HO44-PROJECT/MrJ-HO-scale-DB-style-Era-III-Train-Signals-Electronics/release/kicad_pcb_ho_db_signals_breadboard_v3 - pcb parameters.png

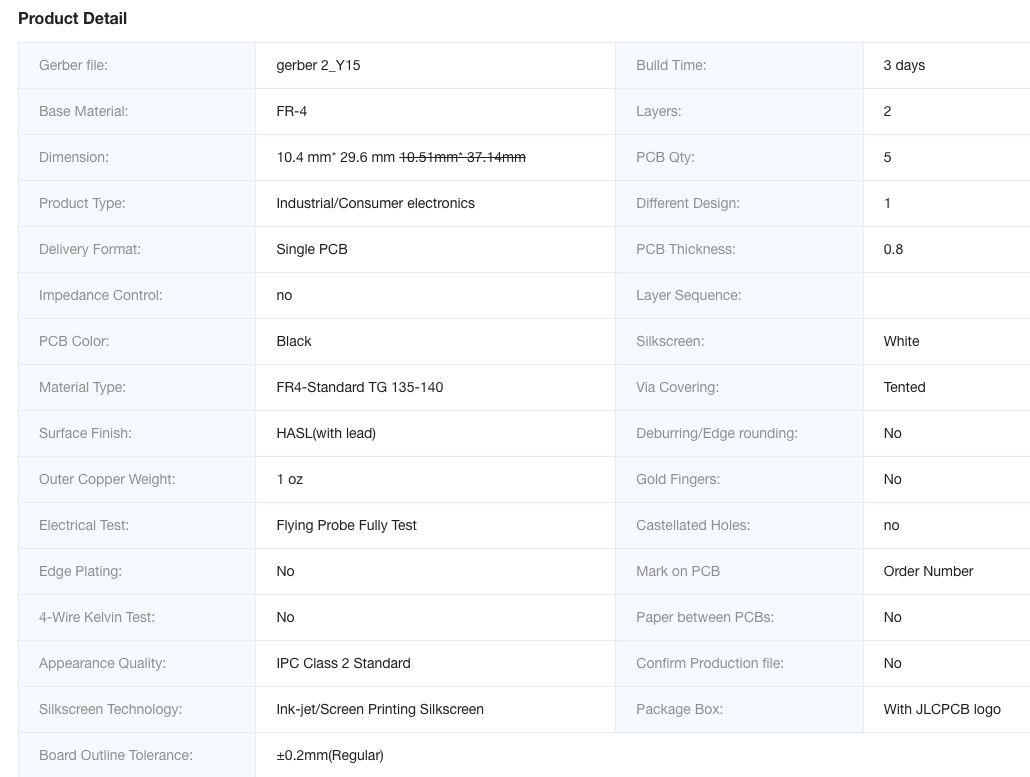
release/kicad_pcb_ho_db_signals_breadboard_v3 - pcb parameters.png
